ikesato/i2c-7segled/i2c-7segled.X/lcd_buffer.c

#include <stdio.h>
#include <stdlib.h>
#include <string.h>
#include "lcd_buffer.h"
#include "defrag_buffer.h"

struct Lbuf {
  char page_num;
  char flip_speed;
  char flip_timer;
  char scroll_enabled;
  char scroll_speed;
  char scroll_timer;
  char scroll_pos;
  char blink_enabled;
  char blink_speed;
  char blink_timer;
  char blink_on;
  char current_page;
  char tmp_buffer[LBUF_TMP_BUFFER_SIZE];
  char lcd[LBUF_LCD_LEN+1];
};

static struct Lbuf lbuf;

static char *lbuf_format_str(char *in, char *out, unsigned char out_size);

void lbuf_init(char *buffer, unsigned char buffer_size) {
  memset(&lbuf, 0, sizeof(lbuf));
  dbuf_init(buffer, buffer_size);
}

void lbuf_reset(void) {
  memset(&lbuf, 0, sizeof(lbuf));
  dbuf_clear();
}

void lbuf_clear(void) {
  dbuf_clear();
}

void lbuf_set_page_num(unsigned char page_num) {
  lbuf.page_num = page_num;
}

void lbuf_set_flip_speed(unsigned char flip_speed) {
  lbuf.flip_speed = flip_speed;
}

void lbuf_set_scroll_speed(unsigned char scroll_speed) {
  lbuf.scroll_speed = scroll_speed;
}

void lbuf_set_blink_speed(unsigned char blink_speed) {
  lbuf.blink_speed = blink_speed;
}

void lbuf_enable_blink(unsigned char enabled) {
  lbuf.blink_enabled = enabled;
}

void lbuf_enable_scroll(unsigned char enabled) {
  lbuf.scroll_enabled = enabled;
}

void lbuf_sync(void) {
  if (lbuf.scroll_enabled) {
    if (lbuf.scroll_timer >= lbuf.scroll_speed) {
      lbuf.scroll_timer = 0;
      lbuf.scroll_pos++;
    } else {
      lbuf.scroll_timer++;
    }
  }
  if (lbuf.page_num > 1) {
    if (lbuf.flip_timer >= lbuf.flip_speed) {
      lbuf.flip_timer = 0;
      lbuf.current_page++;
      if (lbuf.current_page >= lbuf.page_num) {
        lbuf.current_page = 0;
      }
      lbuf.scroll_timer = 0;
      lbuf.scroll_pos = -1;
    } else {
      lbuf.flip_timer++;
    }
  } else {
      lbuf.current_page = 0;
  }
  if (lbuf.blink_enabled) {
    if (lbuf.blink_timer >= lbuf.blink_speed) {
      lbuf.blink_timer = 0;
      lbuf.blink_on = !lbuf.blink_on;
    } else {
      lbuf.blink_timer++;
    }
  }
}

void lbuf_put(int page_no, char *str) {
  str = lbuf_format_str(str, lbuf.tmp_buffer, sizeof(lbuf.tmp_buffer));
  dbuf_put(page_no, str);
}

char *lbuf_get(void) {
  return lbuf.lcd;
}

void lbuf_draw(void) {
  char *str = dbuf_get(lbuf.current_page);
  char slen = strlen(str);
  int i,j;
  int pos;
  if (lbuf.blink_enabled && !lbuf.blink_on) {
    for (i=0; i<LBUF_LCD_LEN; i++) {
      lbuf.lcd[i] = ' ';
    }
    return;
  }

  if (lbuf.scroll_enabled) {
    pos = -(LBUF_LCD_LEN-1);
    pos += lbuf.scroll_pos;
    if (slen < pos) {
      pos -= lbuf.scroll_pos;
      lbuf.scroll_pos = 0;
    }
  } else {
    if (slen > LBUF_LCD_LEN)
      pos = 0;
    else
      pos = -(LBUF_LCD_LEN - slen);
  }
  for (i=0; i<LBUF_LCD_LEN; i++) {
    j = i + pos;
    if (0 <= j && j < slen)
      lbuf.lcd[i] = str[j];
    else
      lbuf.lcd[i] = ' ';
  }
}

static char *lbuf_format_str(char *in, char *out, unsigned char out_size) {
  unsigned char i,j;
  for (i=j=0; in[i] != '\0'; i++, j++) {
    if (in[i] == '.') {
      char c;
      if (i > 0 && in[i-1] != '.') {
        j--;
        c = in[i-1];
      } else {
        c = 0x20;
      }
      if (j < out_size-1)
        out[j] = 0x80 | c;
    } else {
      if (j < out_size-1)
        out[j] = in[i];
    }
  }
  if (j < out_size)
    out[j] = '\0';
  else
    out[out_size-1] = '\0';
  return out;
}

#ifdef DEBUG
void lbuf_print(void) {
  unsigned char i;
  unsigned char c;
  printf("|");
  for (i=0; i<LBUF_LCD_LEN; i++) {
    c = (lbuf.lcd[i] & 0x80 ? '.' : ' ');
    printf("%c%c", lbuf.lcd[i] & 0x7f, c);
  }
  printf("|");
  printf("\r");
  printf("\n");
  fflush(stdout);
}
#endif
