ikesato/i2c-7segled/i2c-7segled.X/seg7lcd.h

#ifndef _SEG7LCD_H_
#define _SEG7LCD_H_

void seg7lcd_init(char *buffer, unsigned char buffer_size);
void seg7lcd_reset(void);
void seg7lcd_clear(void);
void seg7lcd_set_page_num(unsigned char page_num);
void seg7lcd_set_flip_speed(unsigned char flip_speed);
void seg7lcd_set_scroll_speed(unsigned char scroll_speed);
void seg7lcd_set_blink_speed(unsigned char blink_speed);
void seg7lcd_enable_blink(unsigned char enabled);
void seg7lcd_enable_scroll(unsigned char enabled);
void seg7lcd_sync(void);
void seg7lcd_draw(void);
void seg7lcd_puts(int page_no, char *str);

#endif//_SEG7LCD_H_
